makerforceio/KerbalKontrol/code/main-board/io.h

#ifndef IOCUSTOM_H
#define IOCUSTOM_H

#include <avr/io.h>
#include "settings.h"

typedef enum{RESET = 0, SET = 1} PinState_t;
typedef enum{INPUT = 0, OUTPUT = 1} Otype_t;
typedef enum{DISABLE = 0, ENABLE = 1} PuPd_t;

typedef struct 
{
    Otype_t OutputSet;
    PuPd_t PullupSet;
    uint8_t PinSet;

} IO_InitStruct;

void IO_Write(volatile uint8_t *PORTx, uint8_t PINx, PinState_t pinState);
uint8_t IO_Read(volatile uint8_t *PORTx, uint8_t PINx);
void IO_Toggle(volatile uint8_t *PORTx, uint8_t PINx);
void IO_Set(volatile uint8_t *PORTx, uint8_t PINx);
void IO_Clear(volatile uint8_t *PORTx, uint8_t PINx);
void IO_SetDir(volatile uint8_t *DDRx, uint8_t PINx, Otype_t outputType);
void IO_Init(volatile uint8_t *PORTx, volatile uint8_t *DDRx, IO_InitStruct *IO_Init);

#endif /* IOCUSTOM_H */
